bens0n/kara70/plate/pcb_outline.dxf

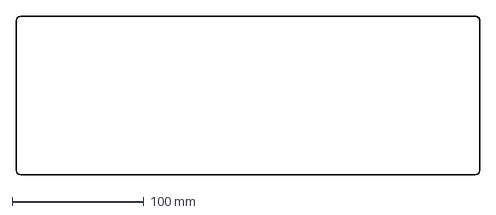
[picture p17: CAD file, 2025-03-10]
plate/pcb_outline.dxf
352.2 x 120.3 mm
