bens0n/kara70/plate/ai03_plate_gen.dxf

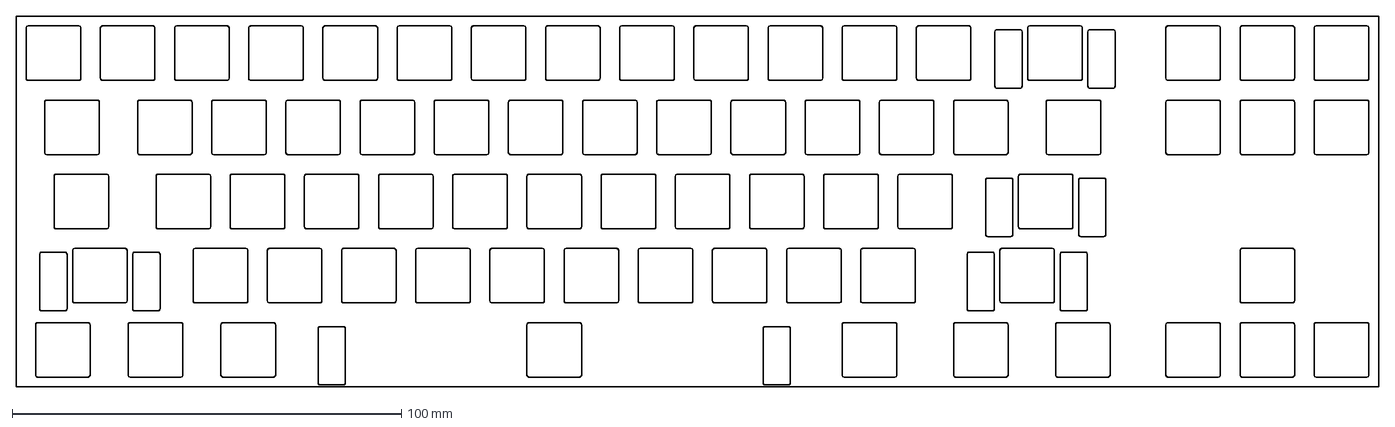
[picture p18: CAD file, 2025-03-10]
plate/ai03_plate_gen.dxf
349.8 x 95.2 mm
